DiegoRosales/Cabinas/Código/botonera/Keypad_I2C/Keypad_I2C.ino

/*  Keypadtest.pde
 *
 *  Demonstrate the simplest use of the  keypad library.
 *
 *  The first step is to connect your keypad to the
 *  Arduino  using the pin numbers listed below in
 *  rowPins[] and colPins[]. If you want to use different
 *  pins then  you  can  change  the  numbers below to
 *  match your setup.
 *
 */
#include <Keypad.h>
#include "Wire.h"

const byte ROWS = 4; // Four rows
const byte COLS = 4; // Three columns
// Define the Keymap
char keys[ROWS][COLS] = {
  {'1','2','3','A'},
  {'4','5','6','B'},
  {'7','8','9','C'},
  {'*','0','#','D'}
};
// Connect keypad ROW0, ROW1, ROW2 and ROW3 to these Arduino pins.
byte rowPins[ROWS] = { 2, 3, 4, 5 }; 
// Connect keypad COL0, COL1 and COL2 to these Arduino pins.
byte colPins[COLS] = { 6, 7, 8, 9 };

// Create the Keypad
Keypad kpd = Keypad( makeKeymap(keys), rowPins, colPins, ROWS, COLS );

#define ledpin 13

void setup()
{
  pinMode(ledpin,OUTPUT);
  digitalWrite(ledpin, HIGH);
  Serial.begin(9600);
  Wire.begin();
}

void loop()
{
  //char key = kpd.getKey();
  char key;

  if(Serial.available()){
    key = Serial.read();
    Serial.println(key);
  }
  if(key)  // Check for a valid key.
  {
    Serial.println("if(key)");
    switch(key){
      case 0:
      case '0':
        Wire.beginTransmission(4); // transmit to device #4
        Wire.write(71);        // sends five bytes
        Wire.endTransmission();    // stop transmitting
        break;
      
      case 'A': /* Red */
        Wire.beginTransmission(4); // transmit to device #4
        Wire.write('7');        // sends five bytes
        Wire.endTransmission();    // stop transmitting
        break;
        
      case 'B': /* Green */
        Wire.beginTransmission(4); // transmit to device #4
        Wire.write('8');        // sends five bytes
        Wire.endTransmission();    // stop transmitting
        break;
        
      case 'C': /* Blue */
        Wire.beginTransmission(4); // transmit to device #4
        Wire.write('9');        // sends five bytes
        Wire.endTransmission();    // stop transmitting
        break;
        
      default:
        Serial.println("switch(key) default");
        Wire.beginTransmission(4); // transmit to device #4
        Wire.write(key);        // sends five bytes
        Wire.endTransmission();    // stop transmitting
        break;
    }
    Serial.println("END switch(key)");
    Serial.println(key, BIN);
    Serial.println("END if(key)");
  }
}
