DiegoRosales/Cabinas/Código/REV 1.5/Controlador_rev_3_0/Const_seq.h

#ifndef CONST_SEQ_H
#define CONST_SEQ_H

const int secuencias[3][20] = {{0x102,//0x081,    //hex 81, dec 129
                    0x212,//0x488,//0x809,   //hex 809, dec 2057
                    0x00A,   //hex 300, dec 768
                    0x502,   //hex 211, dec 529
                    0x410,    //hex 41, dec 65
                    0x054,   //hex 460, dec 1120
                    0xA94,   //hex 448, dec 1096
                    0x080,     //hex E, dec 14
                    0x420,    //hex 81, dec 129
                    0x0A2,   //hex 288, dec 648
                    0x420,    //hex 81, dec 129
                    0x481,   //hex 809, dec 2057
                    0x50A,   //hex 300, dec 768
                    0x002,   //hex 211, dec 529
                    0x410,    //hex 41, dec 65
                    0x054,   //hex 460, dec 1120
                    0x094,   //hex 448, dec 1096
                    0xA80,     //hex E, dec 14
                    0x212,   //hex 244, dec 580
                    0x280},
                    
                    {0x282,   //hex 282, dec 642
                    0x80A,   //hex 80A, dec 2058
                    0x502,   //hex 502, dec 1282
                    0x411,   //hex 411, dec 1041
                    0x281,   //hex 281, dec 641
                    0x4A0,   //hex 4A0, dec 1184
                    0x448,   //hex 448, dec 1096
                    0xE,     //hex E, dec 14
                    0x911,   //hex 911, dec 2321
                    0x308,   //hex 308, dec 776
                    0x82,    //hex 82, dec 130
                    0x80A,   //hex 80A, dec 2058
                    0x500,   //hex 500, dec 1280
                    0x411,   //hex 411, dec 1041
                    0x81,    //hex 81, dec 129
                    0x4A0,   //hex 4A0, dec 1184
                    0x448,   //hex 448, dec 1096
                    0xE,     //hex E, dec 14
                    0x244,   //hex 244, dec 580
                    0xC},
                    
                    {0x284,   //hex 284, dec 644
                    0x80C,   //hex 80C, dec 2060
                    0x902,   //hex 902, dec 2306
                    0x811,   //hex 811, dec 2065
                    0x301,   //hex 301, dec 769
                    0x520,   //hex 520, dec 1312
                    0x44C,   //hex 44C, dec 1100
                    0xA,     //hex A, dec 10
                    0x891,   //hex 891, dec 2193
                    0x288,   //hex 288, dec 648
                    0x84,    //hex 84, dec 132
                    0x80C,   //hex 80C, dec 2060
                    0x900,   //hex 900, dec 2304
                    0x811,   //hex 811, dec 2065
                    0x101,   //hex 101, dec 257
                    0x520,   //hex 520, dec 1312
                    0x448,   //hex 448, dec 1096
                    0xE,     //hex E, dec 14
                    0x244,   //hex 244, dec 580
                    0xC}};

///* SECUENCIA 1 */
//int const seq1[20]={0x102,//0x081,    //hex 81, dec 129
//                    0x212,//0x488,//0x809,   //hex 809, dec 2057
//                    0x00A,   //hex 300, dec 768
//                    0x502,   //hex 211, dec 529
//                    0x410,    //hex 41, dec 65
//                    0x054,   //hex 460, dec 1120
//                    0xA94,   //hex 448, dec 1096
//                    0x080,     //hex E, dec 14
//                    0x420,    //hex 81, dec 129
//                    0x0A2,   //hex 288, dec 648
//                    0x420,    //hex 81, dec 129
//                    0x481,   //hex 809, dec 2057
//                    0x50A,   //hex 300, dec 768
//                    0x002,   //hex 211, dec 529
//                    0x410,    //hex 41, dec 65
//                    0x054,   //hex 460, dec 1120
//                    0x094,   //hex 448, dec 1096
//                    0xA80,     //hex E, dec 14
//                    0x212,   //hex 244, dec 580
//                    0x280};     //hex C, dec 12
//
///* SECUENCIA 2 */                    
//int const seq2[20]={0x282,   //hex 282, dec 642
//                    0x80A,   //hex 80A, dec 2058
//                    0x502,   //hex 502, dec 1282
//                    0x411,   //hex 411, dec 1041
//                    0x281,   //hex 281, dec 641
//                    0x4A0,   //hex 4A0, dec 1184
//                    0x448,   //hex 448, dec 1096
//                    0xE,     //hex E, dec 14
//                    0x911,   //hex 911, dec 2321
//                    0x308,   //hex 308, dec 776
//                    0x82,    //hex 82, dec 130
//                    0x80A,   //hex 80A, dec 2058
//                    0x500,   //hex 500, dec 1280
//                    0x411,   //hex 411, dec 1041
//                    0x81,    //hex 81, dec 129
//                    0x4A0,   //hex 4A0, dec 1184
//                    0x448,   //hex 448, dec 1096
//                    0xE,     //hex E, dec 14
//                    0x244,   //hex 244, dec 580
//                    0xC};     //hex C, dec 12
//
///* SECUENCIA 3 */
//int const seq3[20]={0x284,   //hex 284, dec 644
//                    0x80C,   //hex 80C, dec 2060
//                    0x902,   //hex 902, dec 2306
//                    0x811,   //hex 811, dec 2065
//                    0x301,   //hex 301, dec 769
//                    0x520,   //hex 520, dec 1312
//                    0x44C,   //hex 44C, dec 1100
//                    0xA,     //hex A, dec 10
//                    0x891,   //hex 891, dec 2193
//                    0x288,   //hex 288, dec 648
//                    0x84,    //hex 84, dec 132
//                    0x80C,   //hex 80C, dec 2060
//                    0x900,   //hex 900, dec 2304
//                    0x811,   //hex 811, dec 2065
//                    0x101,   //hex 101, dec 257
//                    0x520,   //hex 520, dec 1312
//                    0x448,   //hex 448, dec 1096
//                    0xE,     //hex E, dec 14
//                    0x244,   //hex 244, dec 580
//                    0xC};     //hex C, dec 12

#endif
