DiegoRosales/Cabinas/Código/Librerías/ShiftReg/ShiftReg.h

/*
 ShiftReg.h - Library for using Mayhew Labs' Mux Shield.
 Created by Mark Mayhew, December 20, 2012.
 Released into the public domain.
 */
#ifndef ShiftReg_h
#define ShiftReg_h

#include "Arduino.h"

#define DIGITAL_IN   0
#define DIGITAL_OUT  1
#define ANALOG_IN    2
#define DIGITAL_IN_PULLUP    3


class ShiftReg
{
public:
    ShiftReg();
    ShiftReg(int S0, int S1, int S2, int S3, int OUTMD,int IOS1, int IOS2, int IOS3, int IO1, int IO2, int IO3);
    void setMode(int mux, int mode);
    void digitalWriteMS(int mux, int chan, int val);
    int digitalReadMS(int mux, int chan);
    int analogReadMS(int mux, int chan);
    
private:
    int _SRCLK,_S1,_S2,_LATCH,_OUTMD,_IOS1,_IOS2,_IOS3,_SERIAL_OUT,_IO2,_IO3;
    int _LE1,_LE2,_LE3,_M1,_M2,_M3;    
    
    
};

#endif
